open-ephys/blinkenbrain/pcb/images/pamphlet-pg1.png

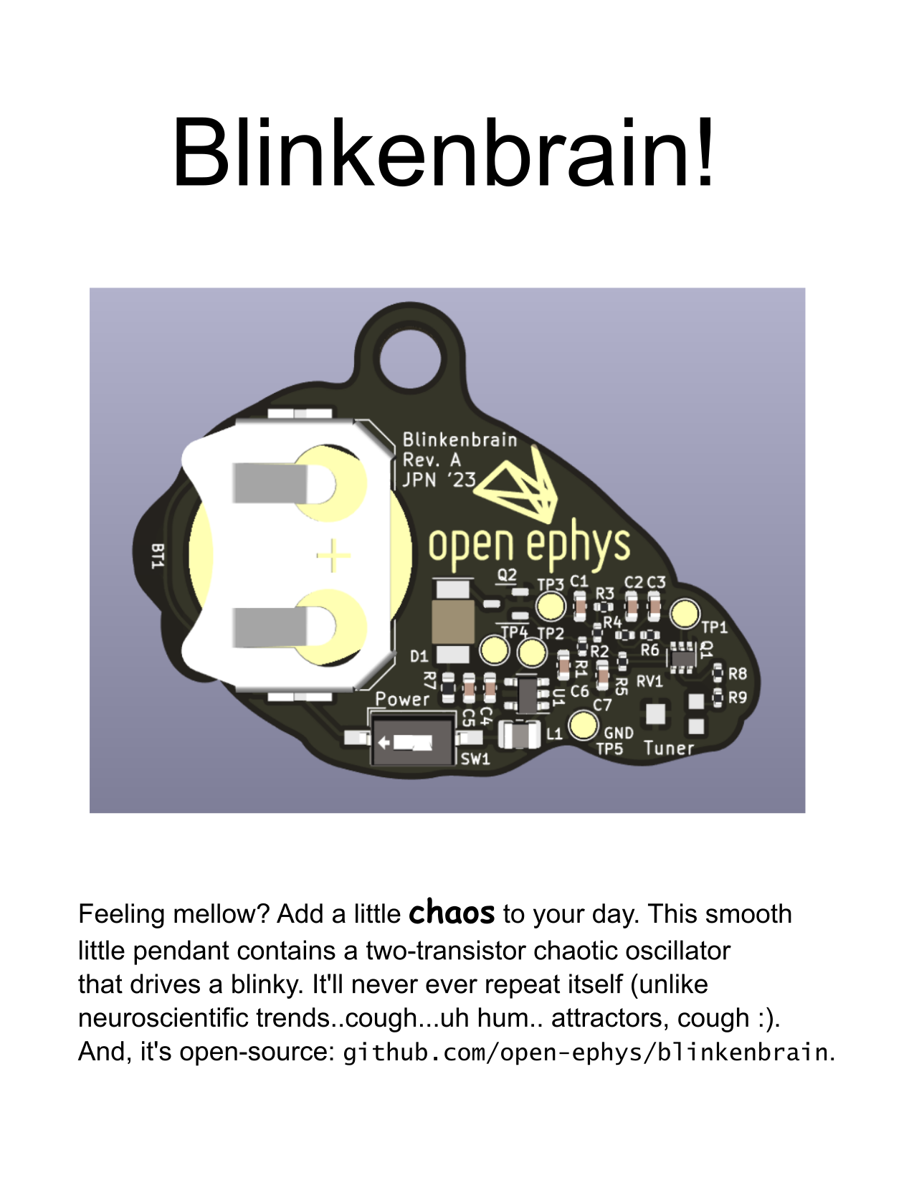
pcb/images/pamphlet-pg1.png
