open-ephys/blinkenbrain/pcb/images/pamphlet-pg2.png

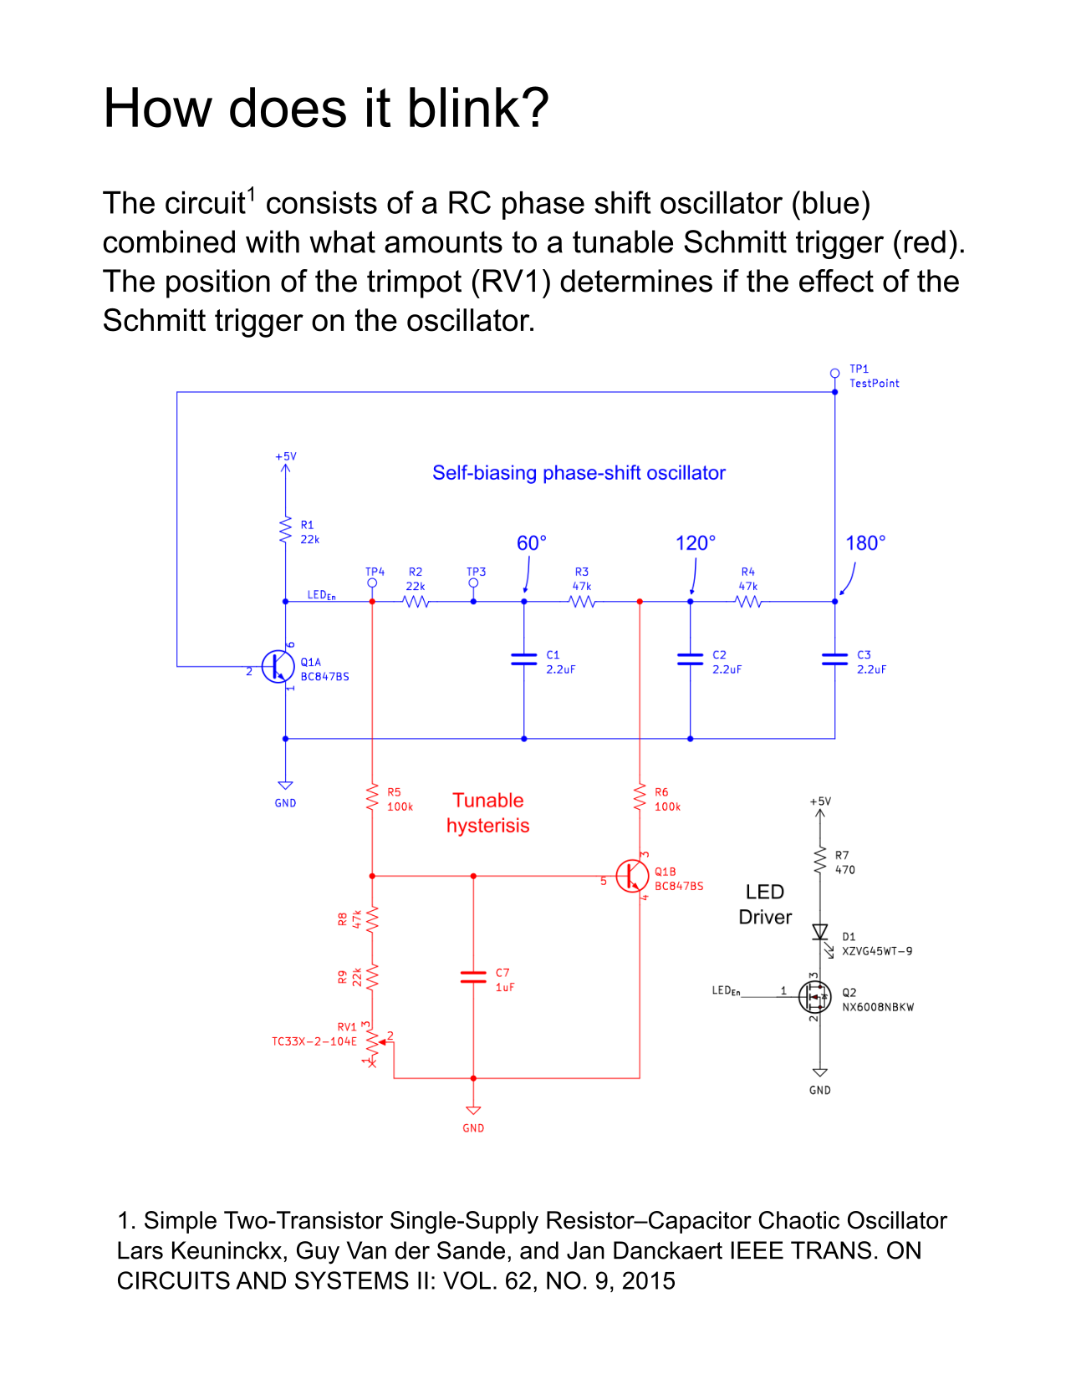
pcb/images/pamphlet-pg2.png
