open-ephys/blinkenbrain/pcb/images/pamphlet-pg4.png

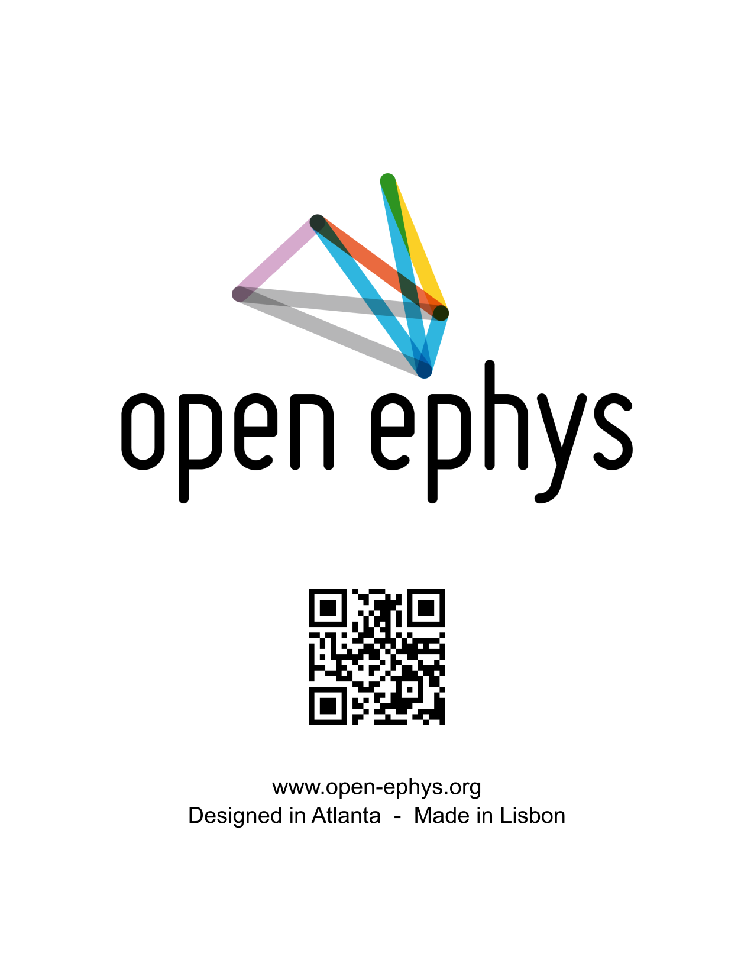
pcb/images/pamphlet-pg4.png
