open-ephys/blinkenbrain/pcb/images/scope_tp4-vs-tp3_02.png

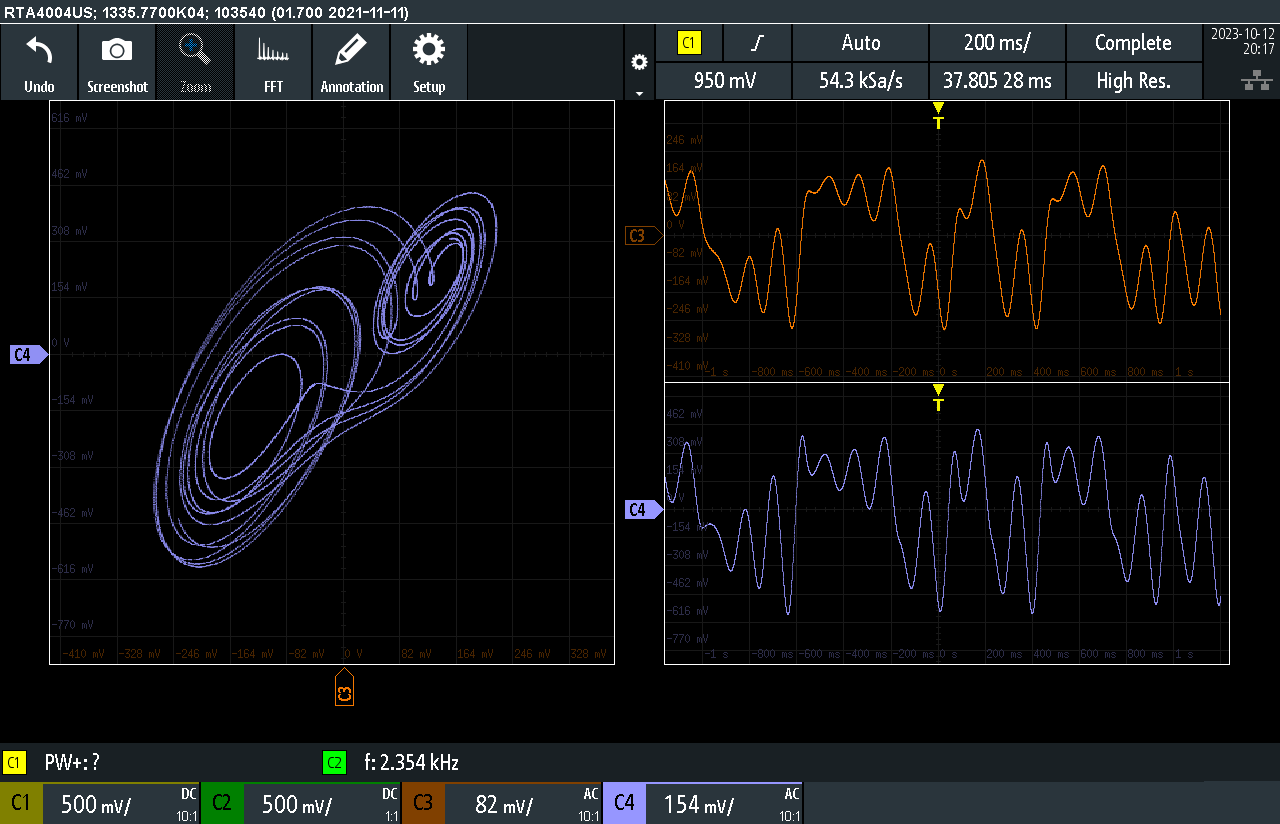
pcb/images/scope_tp4-vs-tp3_02.png
