open-ephys/blinkenbrain/spice/blinkenbrain_rev-d.asc

C1: cap; 2.2µF
C2: cap; 2.2µF
C3: cap; 2.2µF
C4: cap; 1µ
D1: diode; L128-DRD1003500000
Q1: npn; DI_BC847BS
Q2: npn; DI_BC847BS
R1: res; 22k
R2: res; 22k
R3: res; 47k
R4: res; 47k
R5: res; 100k
R6: res; 100k
R7: res; 60k
R8: res; 120
R9: res; 69k
U2: LMV321A
V1: voltage; 5V
Named nets: 0, Vdd, V1, Vce
.tran 60 startup
.MODEL DI_BC847BS  NPN (IS=9.98f NF=1.00 BF=616 VAF=121
+ IKF=60.7m ISE=2.81p NE=2.00 BR=4.00 NR=1.00
+ VAR=20.0 IKR=0.150 RE=0.815 RB=3.26 RC=0.326
+ XTB=1.5 CJE=13.3p VJE=1.10 MJE=0.500 CJC=4.33p VJC=0.300 MJC=0.300 
+ TF=585p TR=49.1n EG=1.12 )
.MODEL DI_BC846AS  NPN (IS=10.1f NF=1.00 BF=301 VAF=145
+ IKF=54.7m ISE=5.50p NE=2.00 BR=4.00 NR=1.00
+ VAR=24.0 IKR=0.135 RE=0.705 RB=2.82 RC=0.282
+ XTB=1.5 CJE=19.1p VJE=1.10 MJE=0.500 CJC=5.37p VJC=0.300
+ MJC=0.300 TF=564p TR=98.4n EG=1.12
