open-ephys/blinkenbrain/spice/chaotic_osc.asc

C1: cap; 1nF
C2: cap; 1nF
C3: cap; 1nF
C4: cap; 360pF
Q1: npn; BC547C
Q2: npn; BC547C
R1: res; 5k
R2: res; 5k
R3: res; 10k
R4: res; 10k
R5: res; 30k
R6: res; 15k
R7: res; 30k
V1: voltage; 5V
Named nets: 0, Vdd
.tran 10m
