open-ephys/blinkenbrain/spice/chaotic_osc_slow_led.asc

C1: cap; 1µF
C2: cap; 1µF
C3: cap; 1µF
C4: cap; 0.47µ
D1: LED; NSPW500BS
Q1: npn; BC547C
Q2: npn; BC547C
R1: res; 20k
R2: res; 20k
R3: res; 40k
R4: res; 40k
R5: res; 120k
R6: res; 60k
R7: res; 190k
U2: Si1012R
V1: voltage; 3.7
Named nets: 0, Vdd, V1, Vce
.tran 10s startup
.step dec param Rt 10k 300k 10
