open-ephys/blinkenbrain/spice/chaotic_osc_slow_led2.asc

C1: cap; 22µF
C2: cap; 22µF
C3: cap; 22µF
C4: cap; 0.47µF
D1: LED; NSPW500BS
Q1: npn; BC547C
Q2: npn; BC547C
R1: res; 2k
R2: res; 1k
R3: res; 1k
R4: res; 2k
R5: res; 5k
R6: res; 6k
R7: res; {Rt}
V1: voltage; 5V
Named nets: 0, Vdd, V1, Vce
.tran 10s startup
.step param Rt 1k 100k 10k
