open-ephys/blinkenbrain/spice/chaotic_osc_slow_led_3V.asc

C1: cap; 1µF
C2: cap; 1µF
C3: cap; 1µF
C4: cap; 0.47µ
D1: LED; NSPW500BS
Q1: npn; BC547C
Q2: npn; BC547C
R1: res; 20k
R2: res; 20k
R3: res; 20k
R4: res; 20k
R5: res; 100k
R6: res; 40k
R7: res; 150k
U2: Si1012R
V1: voltage; 3
Named nets: 0, Vdd, V1, Vce
.tran 10s startup
.step dec param Rt 100k 300k 10
