open-ephys/blinkenbrain/spice/chaotic_osc_slow_led_5V.asc

C1: cap; 1µF
C2: cap; 1µF
C3: cap; 1µF
C4: cap; 0.47µF
Q1: npn; BC847B
Q2: npn; BC847B
R1: res; 20k
R2: res; 20k
R3: res; 40k
R4: res; 40k
R5: res; 120k
R6: res; 60k
R7: res; 170k
R8: res; 1k
U1: Si1012R
V1: voltage; 5V
Named nets: 0, Vdd, V1, Vce
.tran 10s startup
