open-ephys/blinkenbrain/spice/chaotic_osc_slow_led_6V.asc

C1: cap; 1µF
C2: cap; 1µF
C3: cap; 1µF
C4: cap; 2µ
Q1: npn; BC547C
Q2: npn; BC547C
R1: res; 22k
R2: res; 22k
R3: res; 47k
R4: res; 47k
R5: res; 47k
R6: res; 47k
R7: res; 10k
R8: res; 1k
R9: res; 22k
U1: Si1012R
V1: voltage; 6
Named nets: 0, Vdd, V1, Vce
.tran 10s startup
.step param Rt 10k 100k 10k
