open-ephys/blinkenbrain/spice/chua.asc

C1: cap; 0.047µ
C2: cap; 0.0053µ
D1: LED; NSPW500BS
D3: LED; NSPW500BS
L1: ind; 6.8m
Q1: npn; 2N2222
Q2: npn; 2N2222
R1: res; 1.21k
R2: res; 56k
R3: res; 56k
R4: res; 1k
R5: res; 1k
R6: res; 88k
R7: res; 3.3k
R8: res; 3.3k
R9: res; 39k
V1: voltage; 27
Named nets: 0, Vcc, Vc1
.tran 1s
