open-ephys/blinkenbrain/spice/chua1.asc

C1: cap; 0.47
C2: cap; 0.053
D1: LED; NSPW500BS
D3: LED; NSPW500BS
L1: ind; 6.8m
Q1: npn; 2N2222
Q2: npn; 2N2222
R1: res; 100
R2: res; 5.6
R3: res; 5.6
R4: res; 1k
R5: res; 1k
R6: res; 88k
R7: res; 3.3k
R8: res; 3.3k
R9: res; 39k
V1: voltage; 3.7
Named nets: 0, Vcc, Vc1
.tran 10m
