open-ephys/blinkenbrain/spice/minati_circuit.asc

C1: cap; 390p
L1: ind; 150µH
L2: ind; 33µH
Q1: npn; BC547C
R1: res; 1k
V1: voltage; 5V
Named nets: 0, Vcc
.tran 1m startup
