open-ephys/blinkenbrain/spice/minati_fig-4a.asc

1m: ind; 200µ
C1: cap; 10µ
C2: cap; 0.22µ
D1: diode
L2: ind; 200µ
L3: ind; 68µ
Q2: npn; 2N2222
R1: res; 1k
V1: voltage; 3.7
Named nets: Vcc, 0, Vb
.tran 1s startup
.step param Rt 100 2k 200
