open-ephys/blinkenbrain/spice/minati_fig-6.asc

C1: cap; 470p
D1: LED; NSPW500BS
L1: ind; 220µ
L2: ind; 22µ
Q1: npn; 2N3904
Q2: npn; 2N3904
R1: res; {Rt}
R2: res; 0
V1: voltage; 5V
Named nets: Vcc, 0, V1, V2
.tran 1m startup
.step dec param Rt 10 2k 10
.param Rt=1000
