open-ephys/blinkenbrain/spice/minati_fig5.asc

C1: cap; 10n
D1: LED; NSCW100
L1: ind; 68µ
L2: ind; 150µ
L3: ind; 15µ
Q1: npn; BC547C
Q2: npn; BC547C
R2: res; 10
V1: voltage; 5V
Named nets: Vcc, 0
.tran 10m startup
