open-ephys/blinkenbrain/spice/stable_osc.asc

C1: cap; 1nF
C2: cap; 1nF
C3: cap; 1nF
Q1: npn; BC547C
R1: res; 5k
R2: res; 5k
R3: res; 10k
R4: res; 10k
V1: voltage; 5V
Named nets: 0, Vdd
.tran 10m
